Anagha-A26/AMC-Mark-1/STMt1/Images/DRC_Result.png

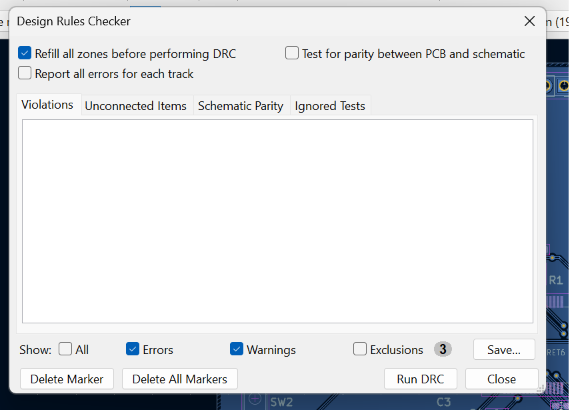
STMt1/Images/DRC_Result.png
